parvg555/chess/Board_BlackBackground.png

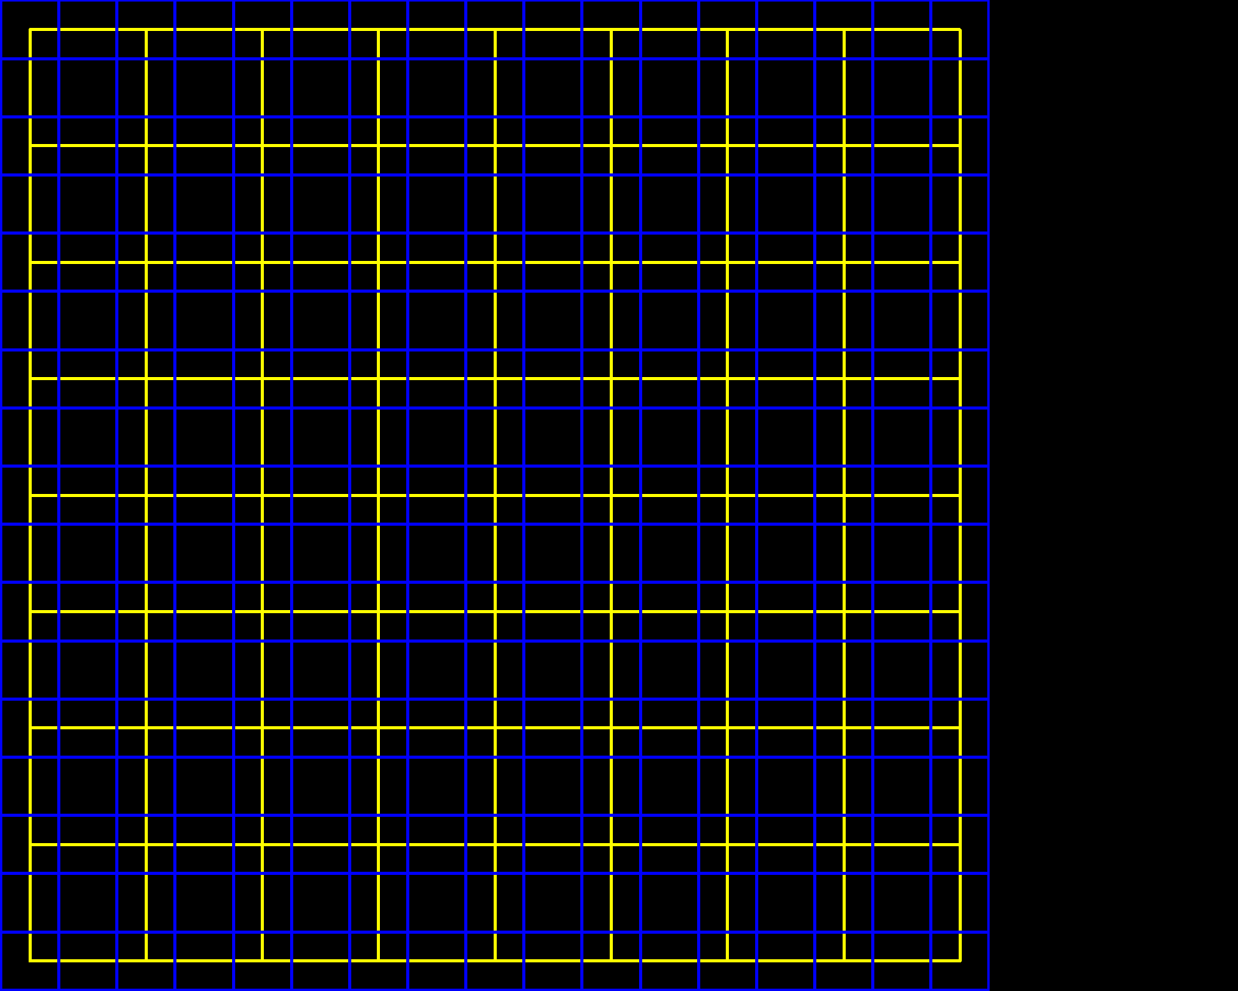
Board_BlackBackground.png
