parvg555/chess/Simulation/sketch_sep19a/sketch_sep19a.ino

#include <Arduino.h>
#include <Vector.h>

int stepPin1 = 2; int dirPin1 = 5;
int stepPin2 = 3; int dirPin2 = 6;
int enable = 8;

///////////////////////////////////////////////////////////////////////////////////////

int motorx = 1;                 // This is the motor number for x-axis movement
int motory = 2;                 // This is the motor number for y-axis movement

int directionx_multiplier = 1;  //set this -1 for counter rotation
int directiony_multiplier = 1;  // set this -1 for counter rotation 

int StepSize = 200;             //number of steps for one box

int x = 0;                      // saves the current position on x axis
int y = 0;						// saves the current position on y axis

//////////////////////////////////////////////////////////////////////////////////////

/* 
	THESE ARE THE RULES DEFINING THE NOMENCLATURE OF EACH PIECE 
	
	1. Unit places of the number defines the color of the piece
		1  -----> White
		2  -----> Black 

	2. Tenth places of the number defines the type of the piece
		1  -----> Pawn
		2  -----> Knight
		3  -----> Bishop
		4  -----> Rook
		5  -----> Queen
		6  -----> King

*/

const int BoardRows = 17;
const int BoardCols = 19;

                            //      0  1  2  3  4  5  6  7  8  9  10 11 12 13 14 15 16 17 18   				
int board[BoardRows][BoardCols] = {{0 ,0 ,0 ,0 ,0 ,0 ,0 ,0 ,0 ,0 ,0 ,0 ,0 ,0 ,0 ,0 ,0 ,0 ,0},     // 0
					 			   {0 ,0 ,41,0 ,21,0 ,31,0 ,61,0 ,51,0 ,31,0 ,21,0 ,41,0 ,0},     // 1
					               {0 ,0 ,0 ,0 ,0 ,0 ,0 ,0 ,0 ,0 ,0 ,0 ,0 ,0 ,0 ,0 ,0 ,0 ,0},     // 2
					               {0 ,0 ,11,0 ,11,0 ,11,0 ,11,0 ,11,0 ,11,0 ,11,0 ,11,0 ,0},	  // 3
					               {0 ,0 ,0 ,0 ,0 ,0 ,0 ,0 ,0 ,0 ,0 ,0 ,0 ,0 ,0 ,0 ,0 ,0 ,0},	  // 4
					               {0 ,0 ,0 ,0 ,0 ,0 ,0 ,0 ,0 ,0 ,0 ,0 ,0 ,0 ,0 ,0 ,0 ,0 ,0},	  // 5
					               {0 ,0 ,0 ,0 ,0 ,0 ,0 ,0 ,0 ,0 ,0 ,0 ,0 ,0 ,0 ,0 ,0 ,0 ,0},	  // 6
					               {0 ,0 ,0 ,0 ,0 ,0 ,0 ,0 ,0 ,0 ,0 ,0 ,0 ,0 ,0 ,0 ,0 ,0 ,0},	  // 7
					               {0 ,0 ,0 ,0 ,0 ,0 ,0 ,0 ,0 ,0 ,0 ,0 ,0 ,0 ,0 ,0 ,0 ,0 ,0},	  // 8
					               {0 ,0 ,0 ,0 ,0 ,0 ,0 ,0 ,0 ,0 ,0 ,0 ,0 ,0 ,0 ,0 ,0 ,0 ,0},	  // 9
					               {0 ,0 ,0 ,0 ,0 ,0 ,0 ,0 ,0 ,0 ,0 ,0 ,0 ,0 ,0 ,0 ,0 ,0 ,0},	  // 10
					               {0 ,0 ,0 ,0 ,0 ,0 ,0 ,0 ,0 ,0 ,0 ,0 ,0 ,0 ,0 ,0 ,0 ,0 ,0},	  // 11
					               {0 ,0 ,0 ,0 ,0 ,0 ,0 ,0 ,0 ,0 ,0 ,0 ,0 ,0 ,0 ,0 ,0 ,0 ,0},	  // 12
					               {0 ,0 ,12,0 ,12,0 ,12,0 ,12,0 ,12,0 ,12,0 ,12,0 ,12,0 ,0},	  // 13
					               {0 ,0 ,0 ,0 ,0 ,0 ,0 ,0 ,0 ,0 ,0 ,0 ,0 ,0 ,0 ,0 ,0 ,0 ,0},	  // 14
					               {0 ,0 ,42,0 ,22,0 ,32,0 ,52,0 ,62,0 ,32,0 ,22,0 ,42,0 ,0},	  // 15
					               {0 ,0 ,0 ,0 ,0 ,0 ,0 ,0 ,0 ,0 ,0 ,0 ,0 ,0 ,0 ,0 ,0 ,0 ,0}};    // 16


//////////////////////////////////////////////////////////////////////////////////////
                 	/* This Portion is for Path finding functions */

struct Point {
	int x;
	int y;
};

Vector <int> dfs() {
	Vector <int> temp;
	return temp;
}


void FindDestination(Point p){
	
}

void move(Point source, Point Destination){
	 
}




/////////////////////////////////////////////////////////////////////////////////////

void setup() {
  	pinMode(stepPin1,OUTPUT); 
  	pinMode(dirPin1,OUTPUT);
    pinMode(stepPin2,OUTPUT); 
    pinMode(dirPin2,OUTPUT);
    pinMode(enable,OUTPUT);
    digitalWrite(enable,LOW);
}

// This function rotates motor - motor steps steps in dxn direction
void rotate(int motor,int steps,int dxn){
    int dirPin,stepPin;
    if(motor==1){
      dirPin=dirPin1;
      stepPin=stepPin1;
    }
    if(motor==2){
      dirPin=dirPin2;
      stepPin=stepPin2;
    }
    if(dxn==1){
      digitalWrite(dirPin,HIGH);
    }
    if(dxn==-1){
      digitalWrite(dirPin,LOW);
    } 
    for(int x = 0; x < steps; x++){
      digitalWrite(stepPin,HIGH);
      delayMicroseconds(10);
      digitalWrite(stepPin,LOW);
      delayMicroseconds(1290);
    }
    delay(1000);
}

// New rotate function to make motors move together 
void RotateBothMotors(int motor1, int motor2, int steps, int dir1, int dir2){
  	int direction_pin1, direction_pin2;
  	int stepper_pin1, stepper_pin2;
  
  	if(motor1 == 1){
    	direction_pin1 = dirPin1;
    	stepper_pin1 = stepPin1;
    	direction_pin2 = dirPin2;
    	stepper_pin2 = stepPin2; 
  	}else{
    	direction_pin1 = dirPin2;
    	stepper_pin1 = stepPin2;
    	direction_pin2 = dirPin1;
    	stepper_pin2 = stepPin1;
  	}

  	if(dir1 == 1){
    	digitalWrite(direction_pin1,HIGH);
  	}else{
    	digitalWrite(direction_pin1,LOW);
  	}
  	if(dir2 == 1){
    	digitalWrite(direction_pin2,HIGH);
  	}else{
    	digitalWrite(direction_pin2,LOW);
  	}
  	for(int i=0;i<steps;i++){
    	digitalWrite(stepper_pin1,HIGH);
    	digitalWrite(stepper_pin2,HIGH);
    	delayMicroseconds(10);
    	digitalWrite(stepper_pin1,LOW);
    	digitalWrite(stepper_pin2,LOW);
    	delayMicroseconds(1290);
  	}
  	delay(1000);
}



// this function is to move foward/up
void u(int steps){
	rotate(motory,steps*StepSize, 1*directiony_multiplier);
	y = y + steps;
}
 
// this function is to move backward/down
void d(int steps){
	rotate(motory,steps*StepSize, -1*directiony_multiplier);
	y = y - steps;
}

// this function is to move in right direction
void r(int steps){
	rotate(motorx, steps*StepSize, 1*directionx_multiplier);
	x = x + steps;
}

// this function is to move in left direction
void l(int steps){
	rotate(motorx,steps*StepSize, -1*directionx_multiplier);
	x = x - steps;
}

// this function is to move in upper right direction
void ur(int steps){
	RotateBothMotors(motorx,motory,steps*StepSize,1*directionx_multiplier, 1*directiony_multiplier);
	x = x + steps;
	y = y + steps;
}

// this function is to move in down right direction
void dr(int steps){
	RotateBothMotors(motorx,motory,steps*StepSize,1*directionx_multiplier, -1*directiony_multiplier);
	x = x + steps;
	y = y - steps;
}

// this function is to move in down left direction
void dl(int steps){
	RotateBothMotors(motorx,motory,steps*StepSize,-1*directionx_multiplier,-1*directiony_multiplier);
	x = x - steps;
	y = y - steps;

}

// this function is to move in upper left direction
void ul(int steps){
	RotateBothMotors(motorx,motory,steps*StepSize,-1*directionx_multiplier,1*directiony_multiplier);
	x = x - steps;
	y = y + steps;
}

void loop(){
	u(1);
	delay(1000);
	ur(1);
	delay(1000);
	r(1);
  	delay(1000);
  	dr(1);
  	delay(1000);
  	d(1);
  	delay(1000);
  	dl(1);
  	delay(1000);
  	l(1);
  	delay(1000);
  	ul(1);
  	delay(1000);
  	u(1);
  	delay(1000);
}
